kmakise/EducationPhysicalExaminationPlatform/MCUProject/Hardware/OLED/oled.h

#ifndef __OLED_H
#define __OLED_H			  	 
#include "stdlib.h"	 
#include "main.h"
#include "stm32f4xx_hal.h"

#define u8 uint8_t
#define u16 uint16_t
#define u32 uint32_t

#define OLED_MODE 0
#define SIZE 8
#define XLevelL		0x00
#define XLevelH		0x10
#define Max_Column	128
#define Max_Row		64
#define	Brightness	0xFF 
#define X_WIDTH 	128
#define Y_WIDTH 	64	    						  
//-----------------OLED IIC端口定义----------------  					   

#define OLED_SCLK_Clr() HAL_GPIO_WritePin(OLED_SCL_GPIO_Port,OLED_SCL_Pin,GPIO_PIN_RESET) //SCL
#define OLED_SCLK_Set() HAL_GPIO_WritePin(OLED_SCL_GPIO_Port,OLED_SCL_Pin,GPIO_PIN_SET)

#define OLED_SDIN_Clr() HAL_GPIO_WritePin(OLED_SDA_GPIO_Port,OLED_SDA_Pin,GPIO_PIN_RESET)//SDA
#define OLED_SDIN_Set() HAL_GPIO_WritePin(OLED_SDA_GPIO_Port,OLED_SDA_Pin,GPIO_PIN_SET)

 		     
#define OLED_CMD  0	//写命令
#define OLED_DATA 1	//写数据

//OLED控制用函数
void fill_picture(unsigned char fill_Data);
void OLED_Set_Pos(unsigned char x, unsigned char y);
void OLED_Display_On(void);
void OLED_Display_Off(void);
void OLED_Clear(void);
void OLED_On(void) ;
void OLED_ShowChar(u8 x,u8 y,u8 chr,u8 Char_Size);
void OLED_ShowNum(u8 x,u8 y,u32 num,u8 len,u8 size2);
void OLED_ShowString(u8 x,u8 y,u8 *chr,u8 Char_Size);
void OLED_DrawBMP(unsigned char x0, unsigned char y0,unsigned char x1, unsigned char y1,unsigned char BMP[]);

void OLED_Init(void);

#endif  
	 
